Thynix/feather-audio/include/display.h

// Boot status messages for the bottom line.
const char* const booting    = "Boot";
const char* const boot_error = "Boot error";

bool display_setup();
bool display_text(const char* top, const char* bottom);
